timhodgson12/pomodoro/wiring/IMG_9831.jpg

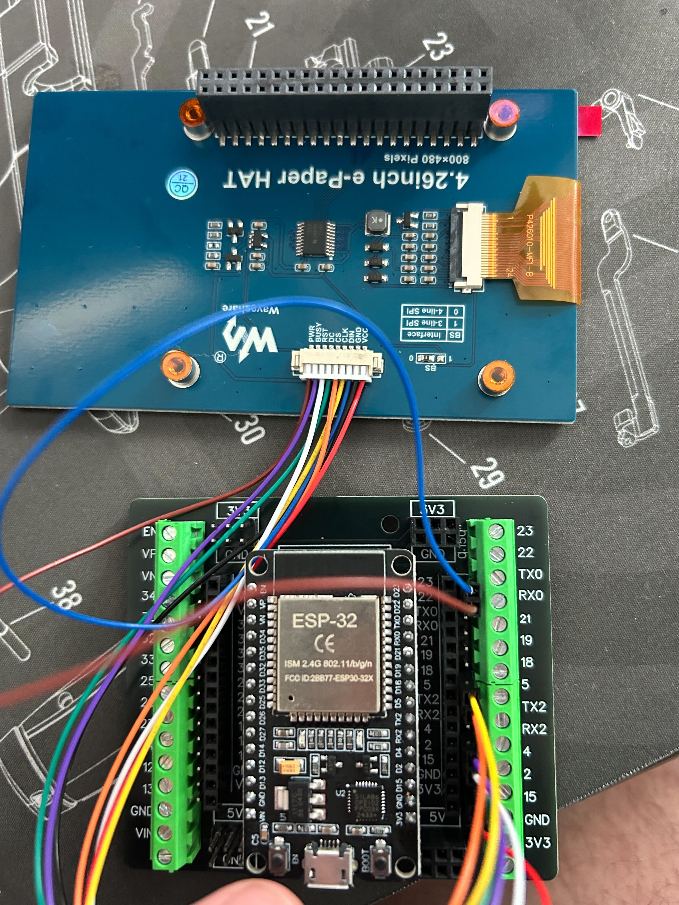
wiring/IMG_9831.jpg
