timhodgson12/pomodoro/src/icons.h

#ifndef ICONS_H
#define ICONS_H

#include "icon.h"

extern Icon icon_lpethink;
extern Icon icon_email;
extern Icon icon_checkmark;
extern Icon icon_lpenote;
extern Icon icon_lpetantrum;
extern Icon icon_lpehacker;
extern Icon icon_coding;
extern Icon icon_lpesip;
extern Icon icon_focus;
extern Icon icon_coffee;

#endif // ICONS_H
