timhodgson12/pomodoro/src/images.h

#ifndef IMAGES_H
#define IMAGES_H

#include "images/image_bg_lpe_bubble.h"
#include "images/image_bg_what_a_week.h"
#include "images/image_bg_bubble.h"
#include "images/image_bg_splash.h"
#include "images/image_bg_pablo.h"
#include "images/image_bg_stonks.h"
#include "images/image_bg_cat.h"

#endif // IMAGES_H
