timhodgson12/pomodoro/src/splashscreen.h

#ifndef SPLASHSCREEN_H
#define SPLASHSCREEN_H

#include <Arduino.h>
#include <GxEPD2_BW.h>
#include <GxEPD2_GFX.h>
#include "gfx_utils.h"
#include "icons.h"
#include "icon.h"
#include "timer.h"
#include "checkbox.h"
#include "debug.h"
#include "images.h"
#include <vector>

class SplashScreen
{
private:
    DISPLAY_CLASS &display;
    Timer &timer;

    Menu buttons = Menu(display, new MenuItem[2]{MenuItem("Start"), MenuItem("Einstellungen")}, 2);

    std::vector<Checkbox> checkboxes = {
        Checkbox(&icon_lpehacker, "LPE Modus", "lpe", true),
        Checkbox(&icon_lpenote, "Ablenkende Nachrichten", "msgs", true),
        Checkbox(nullptr, "Reset Device", "reset"),
    };

    Checkbox *selectedCheckbox;
    int16_t selectedSettingsIndex = 0;
    int16_t lastEncoderCount = 0;

public:
    SplashScreen(DISPLAY_CLASS &display, Timer &timer);
    ~SplashScreen();
    void setLastEncoderCount(int16_t count);
    void draw();
    void loop(volatile int *encoderCount);

    void drawSettings();
    void loopSettings(volatile int *encoderCount);
};

#endif
